nazililham11/smart_street_lights-arduino/Assets/(2).jpeg

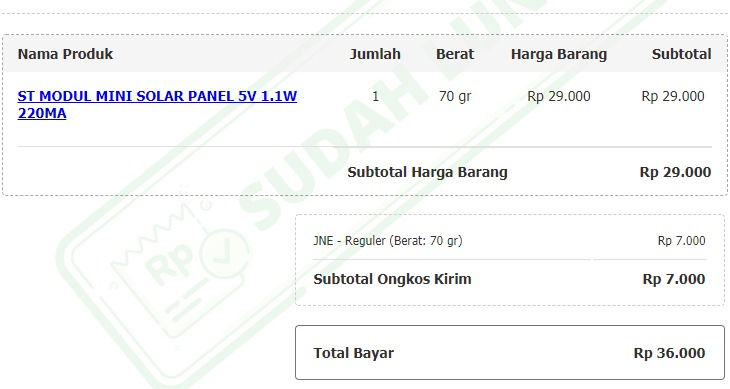
Assets/(2).jpeg
