nazililham11/smart_street_lights-arduino/Assets/(3).jpg

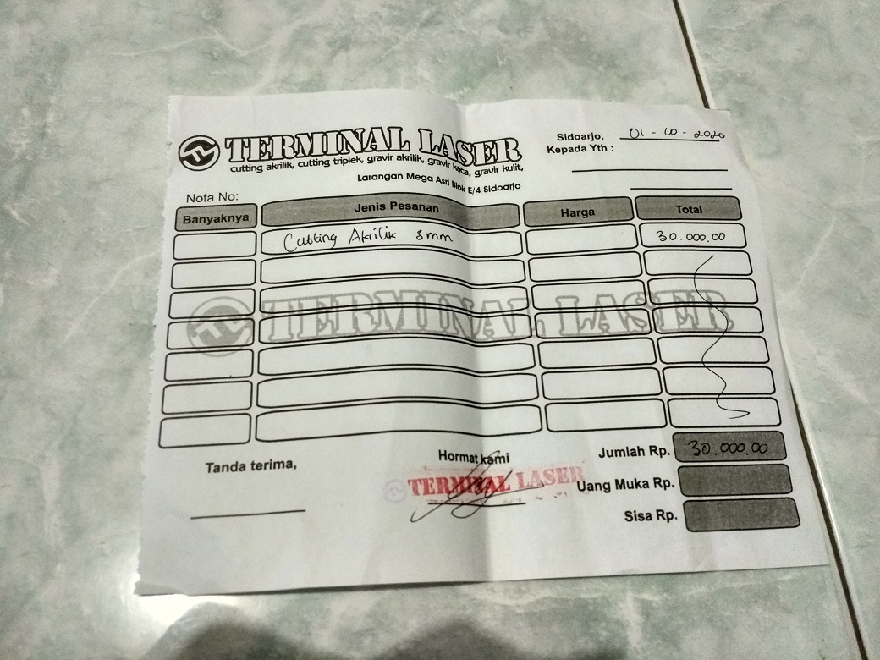
Assets/(3).jpg
