nazililham11/smart_street_lights-arduino/Assets/(4).jpeg

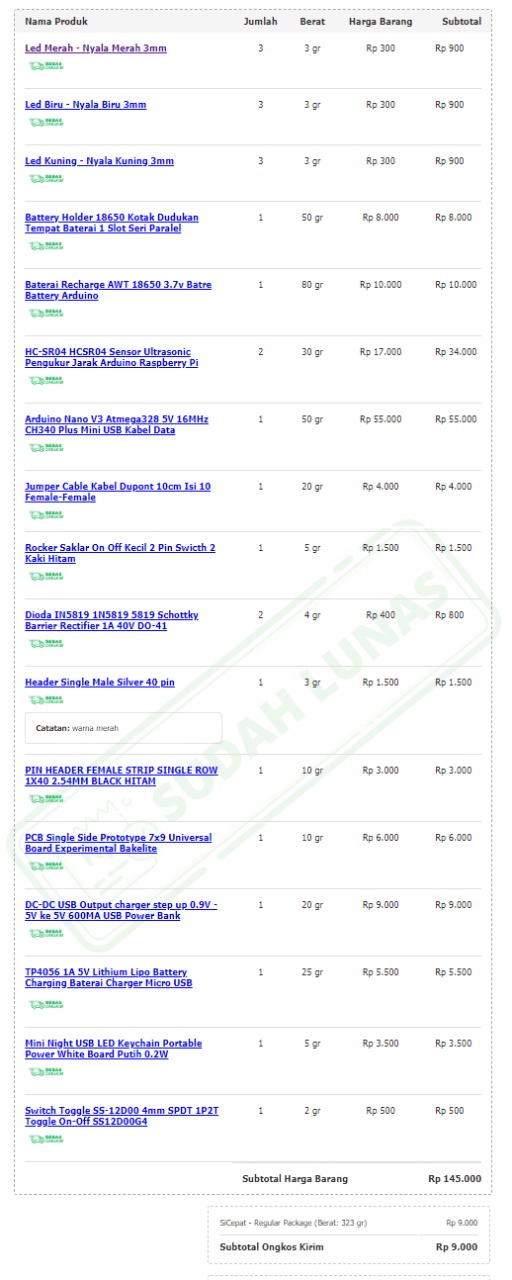
Assets/(4).jpeg
